xoseperez/rak833-hat/images/20180626_130729.jpg

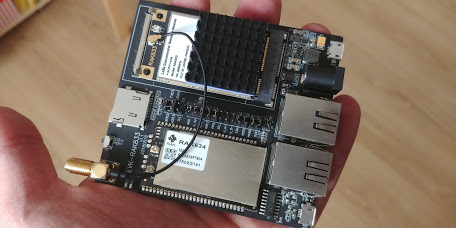
images/20180626_130729.jpg
