xoseperez/rak833-hat/images/20180702_132220.jpg

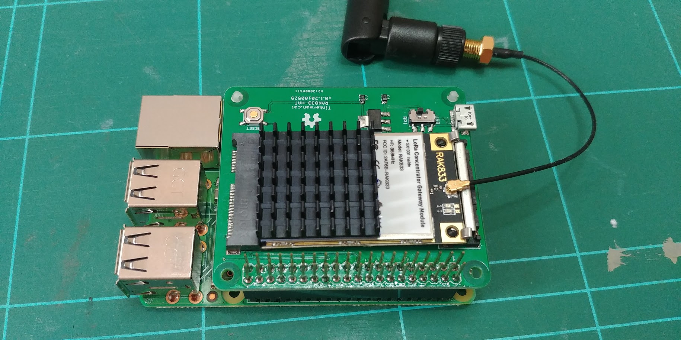
images/20180702_132220.jpg
