xoseperez/rak833-hat/images/20180702_132230.jpg

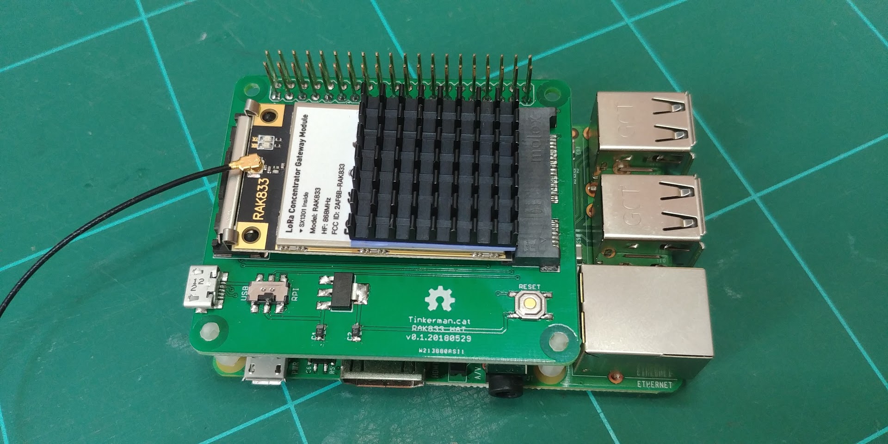
images/20180702_132230.jpg
